drmoratorius/steampunk-hat/KiCAD/Steampunk Hat.kicad_sch

## KiCad design KiCAD/Steampunk Hat.kicad_sch (2024-03-11)

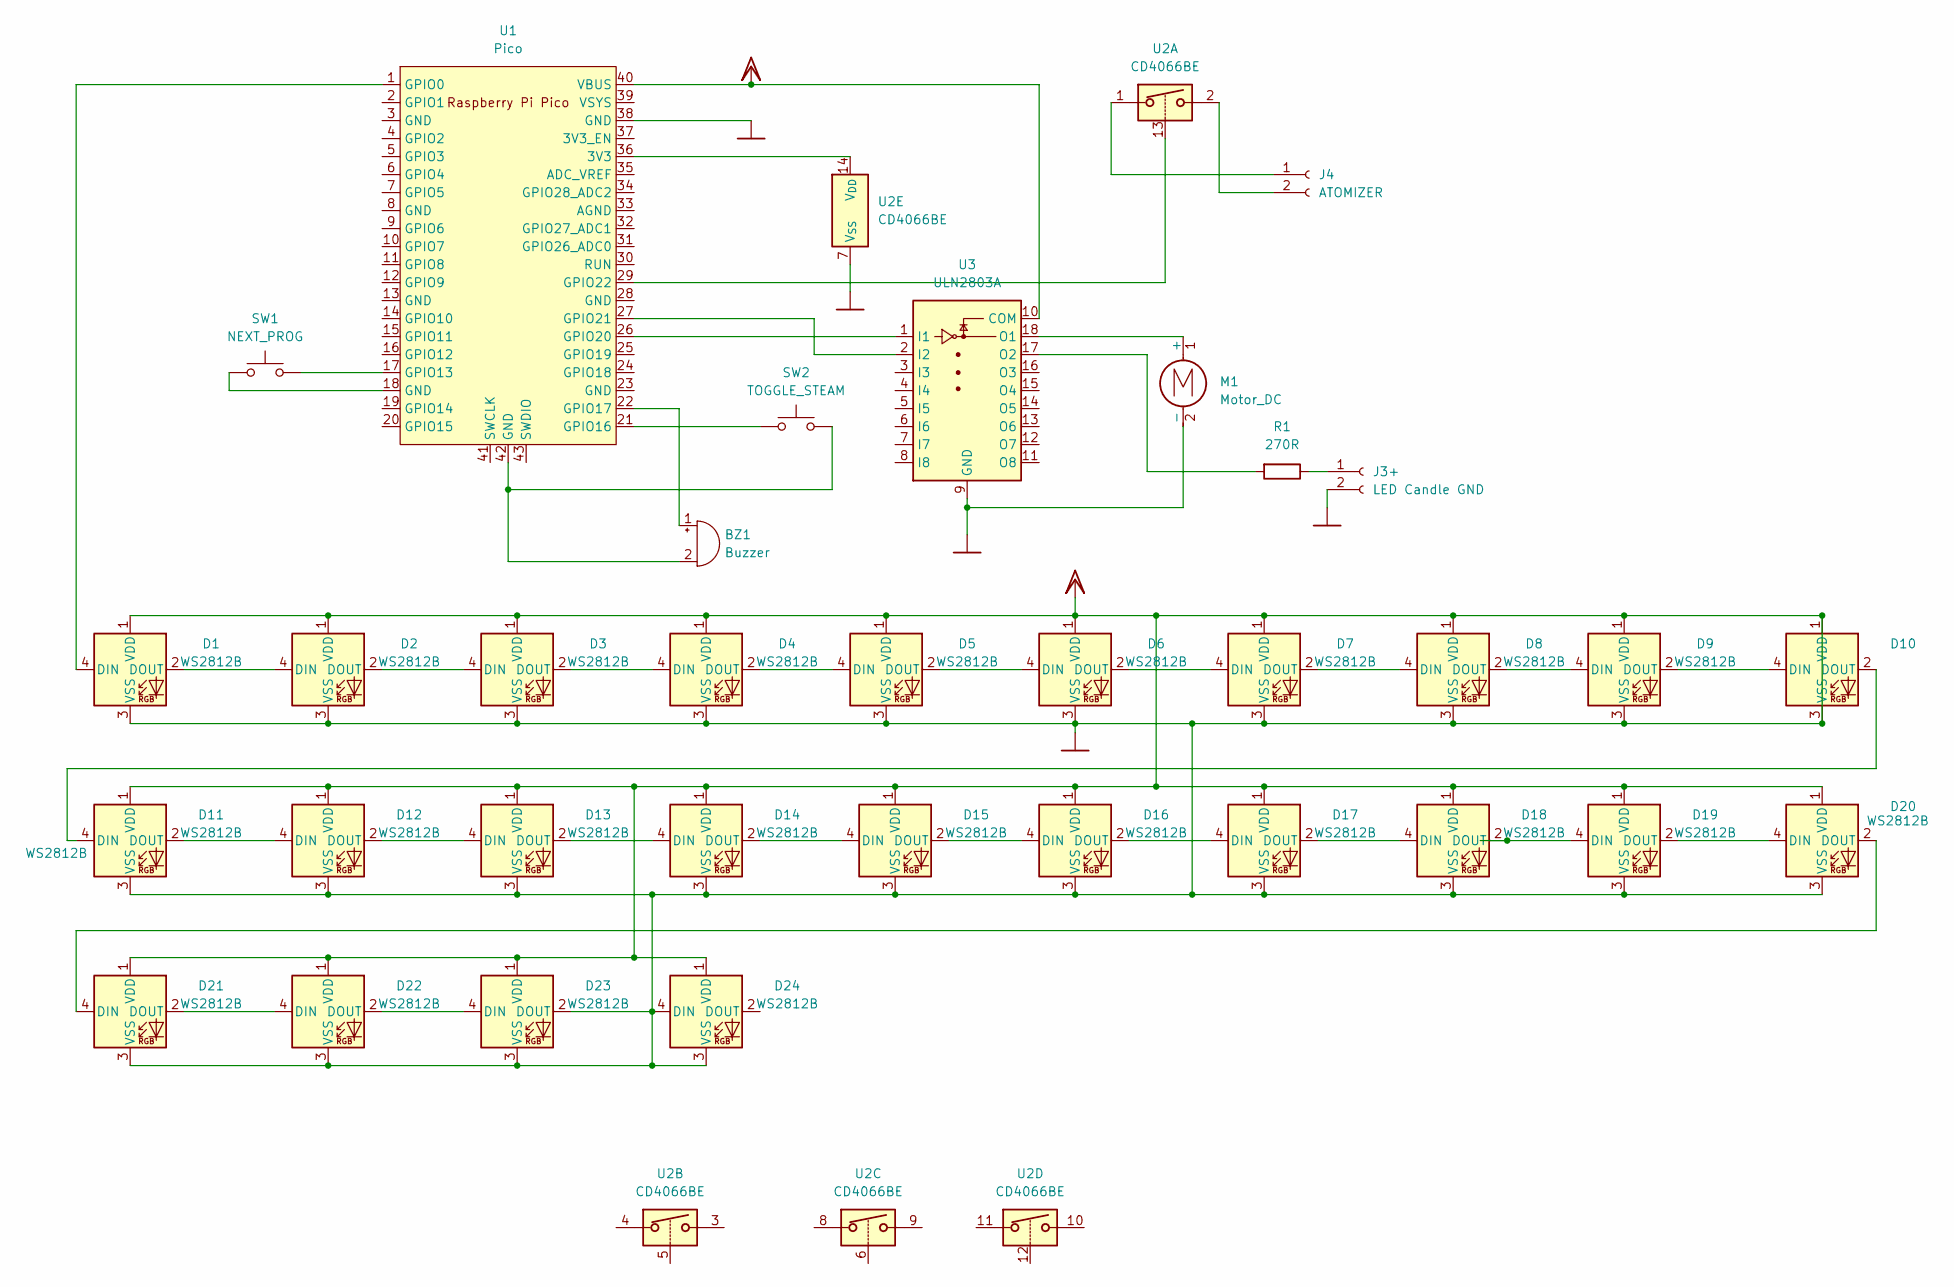
[picture p25: schematic Steampunk Hat.kicad_sch]

Parts:
BZ1: Buzzer
D1, D2, D3, D4, D5, D6, D7, D8, D9, D10, D11, D12, D13, D14, D15, D16, D17, D18, D19, D20, D21, D22, D23, D24: WS2812B; LED_WS2812B_PLCC4_5.0x5.0mm_P3.2mm
J3+: LED Candle GND
J4: ATOMIZER
M1: Motor_DC
R1: 270R
SW1: NEXT_PROG
SW2: TOGGLE_STEAM
U1: Pico; RPi_Pico_SMD_TH
U2: CD4066BE; DIP-14_W7.62mm
U3: ULN2803A

Connections:
unnamed: BZ1.1 (+), U1.22 (GPIO17)
unnamed: BZ1.2 (-), SW2.2, U1.42 (GND)
unnamed: D1.2 (DOUT), D2.4 (DIN)
unnamed: D1.4 (DIN), U1.1 (GPIO0)
unnamed: D2.2 (DOUT), D3.4 (DIN)
unnamed: D3.2 (DOUT), D4.4 (DIN)
unnamed: D4.2 (DOUT), D5.4 (DIN)
unnamed: D5.2 (DOUT), D6.4 (DIN)
unnamed: D6.2 (DOUT), D7.4 (DIN)
unnamed: D7.2 (DOUT), D8.4 (DIN)
unnamed: D8.2 (DOUT), D9.4 (DIN)
unnamed: D10.2 (DOUT), D11.4 (DIN)
unnamed: D9.2 (DOUT), D10.4 (DIN)
unnamed: D11.2 (DOUT), D12.4 (DIN)
unnamed: D12.2 (DOUT), D13.4 (DIN)
unnamed: D13.2 (DOUT), D14.4 (DIN)
unnamed: D14.2 (DOUT), D15.4 (DIN)
unnamed: D15.2 (DOUT), D16.4 (DIN)
unnamed: D16.2 (DOUT), D17.4 (DIN)
unnamed: D17.2 (DOUT), D18.4 (DIN)
unnamed: D18.2 (DOUT), D19.4 (DIN)
unnamed: D19.2 (DOUT), D20.4 (DIN)
unnamed: D20.2 (DOUT), D21.4 (DIN)
unnamed: D21.2 (DOUT), D22.4 (DIN)
unnamed: D22.2 (DOUT), D23.4 (DIN)
unnamed: J3+.1, R1.1
unnamed: J4.1, U2.1
unnamed: J4.2, U2.2
unnamed: M1.1 (+), U3.18 (O1)
unnamed: R1.2, U3.17 (O2)
unnamed: SW1.1, U1.18 (GND)
unnamed: SW1.2, U1.17 (GPIO13)
unnamed: SW2.1, U1.21 (GPIO16)
unnamed: U1.26 (GPIO20), U3.1 (I1)
unnamed: U1.27 (GPIO21), U3.2 (I2)
unnamed: U1.29 (GPIO22), U2.13
unnamed: U1.36 (3V3), U2.14 (V_{DD})
~: D1.1 (VDD), D1.3 (VSS), D2.1 (VDD), D2.3 (VSS), D3.1 (VDD), D3.3 (VSS), D4.1 (VDD), D4.3 (VSS), D5.1 (VDD), D5.3 (VSS), D6.1 (VDD), D6.3 (VSS), D7.1 (VDD), D7.3 (VSS), D8.1 (VDD), D8.3 (VSS), D9.1 (VDD), D9.3 (VSS), D10.1 (VDD), D10.3 (VSS), D11.1 (VDD), D11.3 (VSS), D12.1 (VDD), D12.3 (VSS), D13.1 (VDD), D13.3 (VSS), D14.1 (VDD), D14.3 (VSS), D15.1 (VDD), D15.3 (VSS), D16.1 (VDD), D16.3 (VSS), D17.1 (VDD), D17.3 (VSS), D18.1 (VDD), D18.3 (VSS), D19.1 (VDD), D19.3 (VSS), D20.1 (VDD), D20.3 (VSS), D21.1 (VDD), D21.3 (VSS), D22.1 (VDD), D22.3 (VSS), D23.1 (VDD), D23.2 (DOUT), D23.3 (VSS), D24.1 (VDD), D24.3 (VSS), D24.4 (DIN), J3+.2, M1.2 (-), U1.38 (GND), U1.40 (VBUS), U2.7 (V_{SS}), U3.9 (GND), U3.10 (COM)
